OpenSourceNeuro/IssaScope/GUI/PyQt/resources/Droso2.png

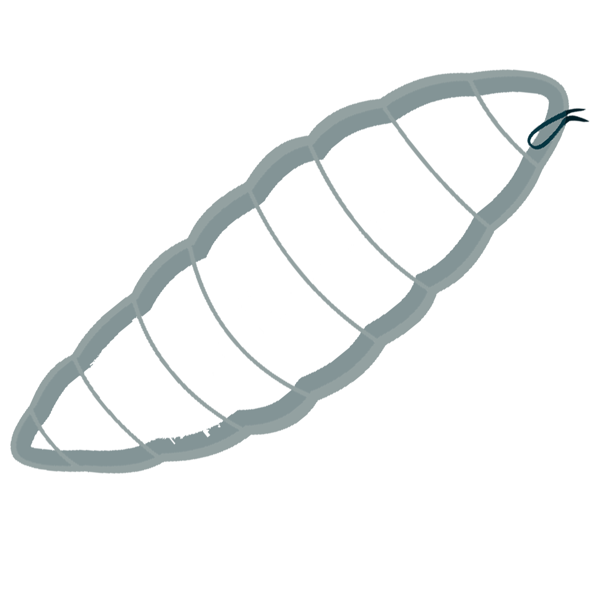
GUI/PyQt/resources/Droso2.png
