OpenSourceNeuro/IssaScope/GUI/PyQt/resources/Droso.png

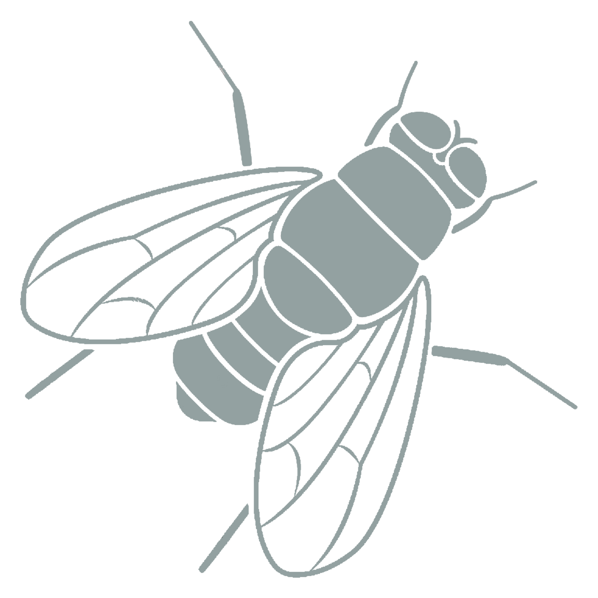
GUI/PyQt/resources/Droso.png
