OpenSourceNeuro/IssaScope/GUI/PyQt/resources/Issa.png

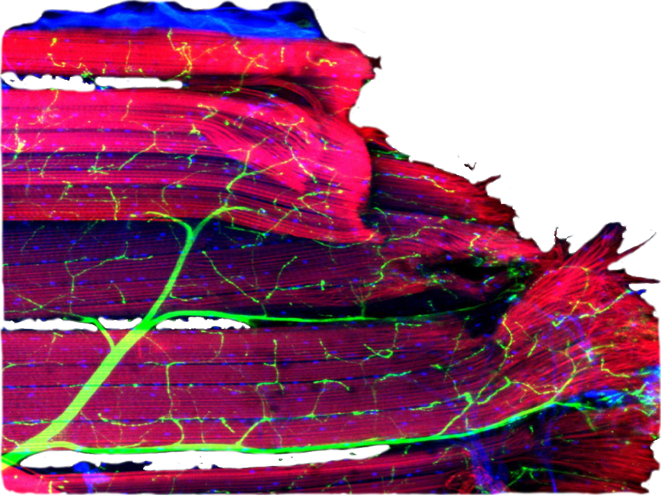
GUI/PyQt/resources/Issa.png
